KCSAbeywickrama/rgb-g2/enclosure/external parts/push button/Captura de pantalla (63).png

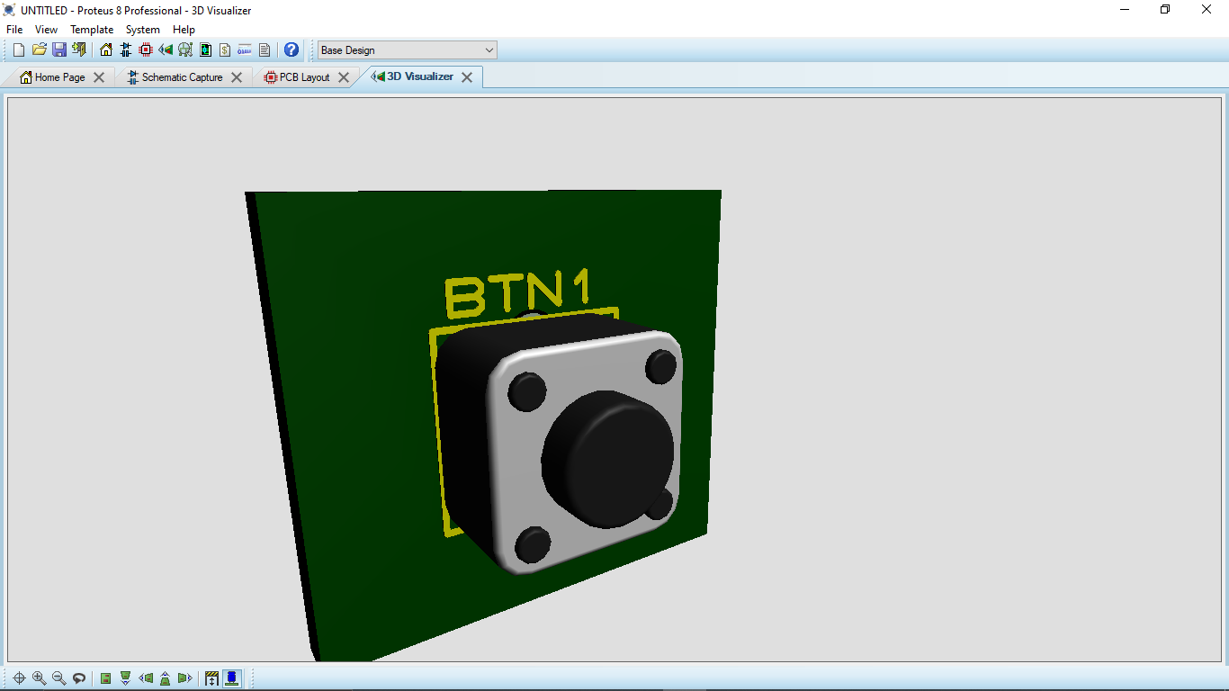
enclosure/external parts/push button/Captura de pantalla (63).png
