KCSAbeywickrama/rgb-g2/enclosure/external parts/capacitor/10pF Ceramic Disc 2.SLDPRT

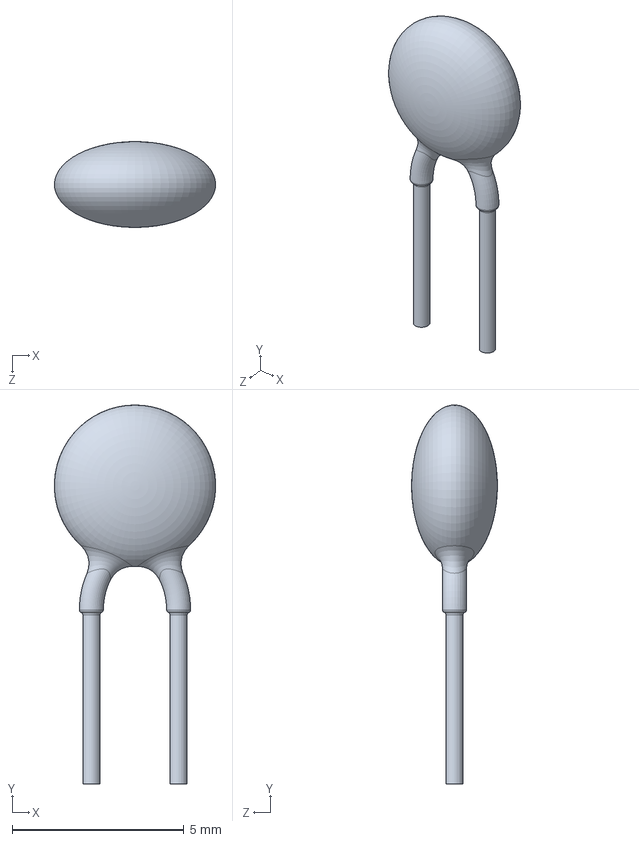
[picture p18: CAD file, 2021-08-13]
enclosure/external parts/capacitor/10pF Ceramic Disc 2.SLDPRT
4.69 x 11.0 x 2.50 mm
