KCSAbeywickrama/rgb-g2/enclosure/external parts/jumper/Converted/ACIS/Wire.step

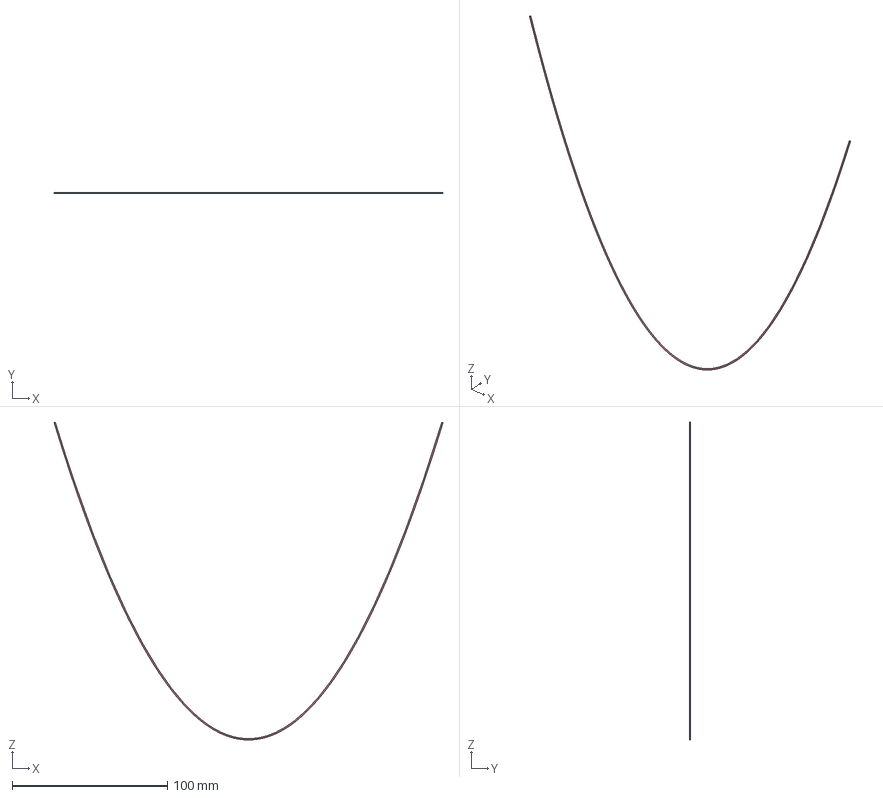
[picture p19: CAD file, 2021-08-13]
enclosure/external parts/jumper/Converted/ACIS/Wire.step
250.8 x 0.9 x 205.0 mm
15cm
20cm
30cm
50cm
