KCSAbeywickrama/rgb-g2/enclosure/external parts/power jack/power jack.SLDPRT

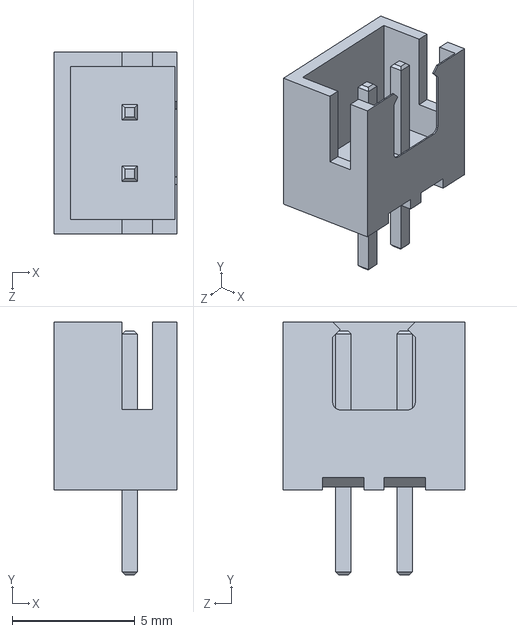
[picture p20: CAD file, 2021-08-13]
enclosure/external parts/power jack/power jack.SLDPRT
5.00 x 10.3 x 7.43 mm
