KCSAbeywickrama/rgb-g2/enclosure/external parts/push button/2_pin_push_button.SLDPRT

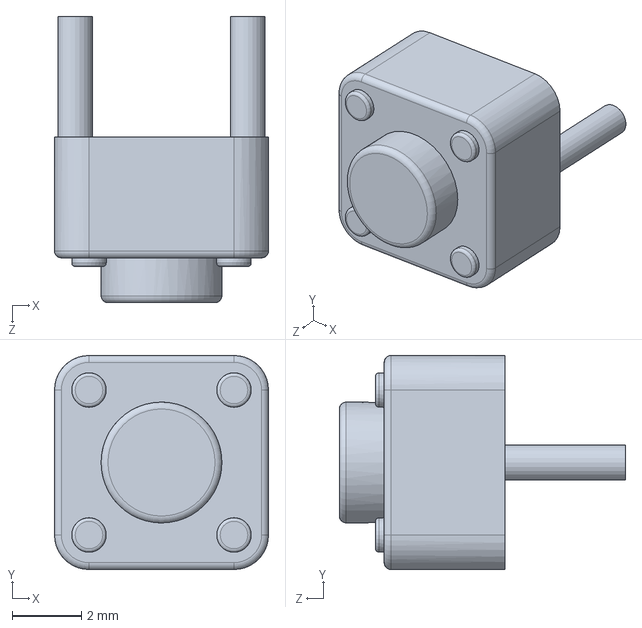
[picture p21: CAD file, 2021-08-13]
enclosure/external parts/push button/2_pin_push_button.SLDPRT
6.20 x 6.20 x 8.30 mm
