KCSAbeywickrama/rgb-g2/enclosure/external parts/rgb led/rgb_led.SLDPRT

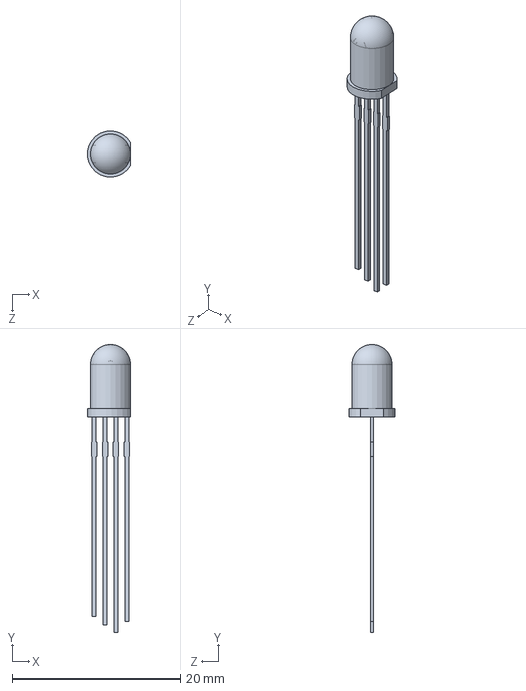
[picture p22: CAD file, 2021-08-13]
enclosure/external parts/rgb led/rgb_led.SLDPRT
5.10 x 34.2 x 5.49 mm
