KCSAbeywickrama/rgb-g2/enclosure/external parts/solder.SLDPRT

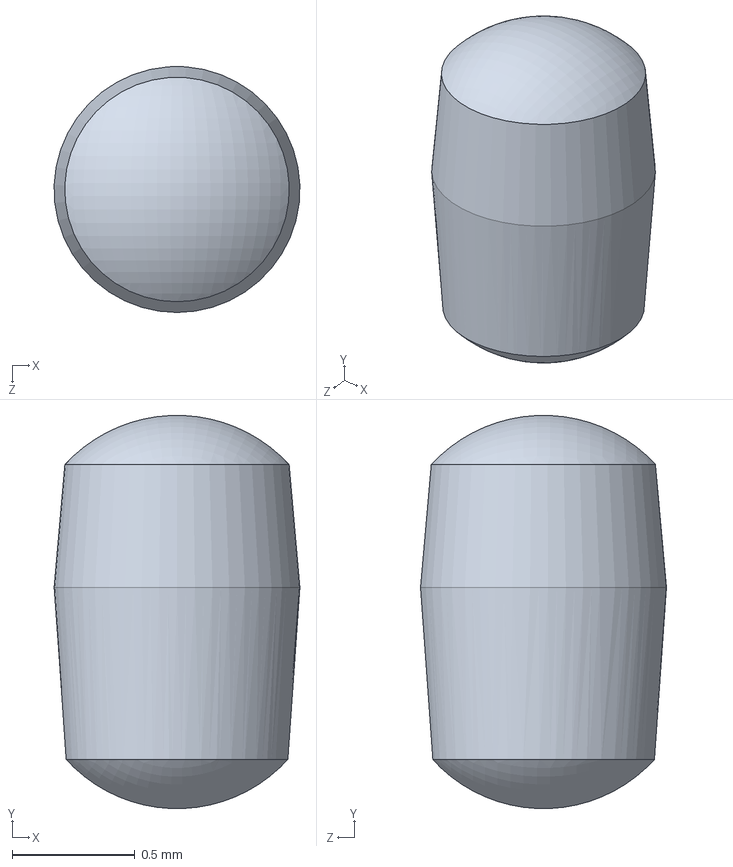
[picture p23: CAD file, 2021-08-13]
enclosure/external parts/solder.SLDPRT
0.999 x 1.60 x 1.00 mm
