KCSAbeywickrama/rgb-g2/enclosure/Model_2_upper_stp.STEP

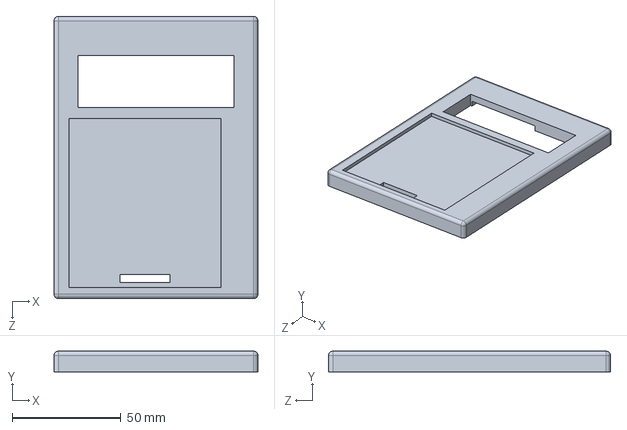
[picture p24: CAD file, 2021-08-13]
enclosure/Model_2_upper_stp.STEP
94.0 x 9.50 x 130.0 mm
