KCSAbeywickrama/rgb-g2/enclosure/Sensor/Sensor_Top.STEP

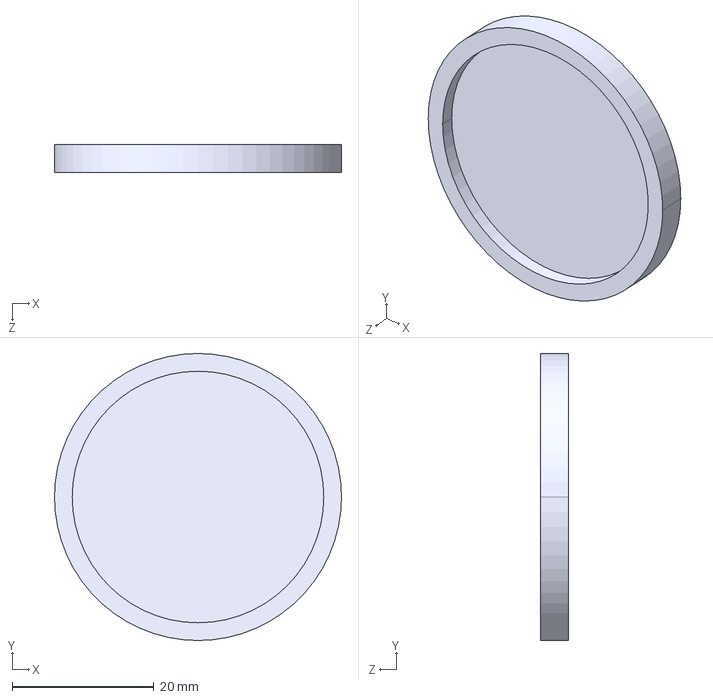
[picture p25: CAD file, 2021-08-13]
enclosure/Sensor/Sensor_Top.STEP
40.5 x 40.5 x 4.00 mm
