KCSAbeywickrama/rgb-g2/pcb_design/STEP files/HDR1X6.STEP

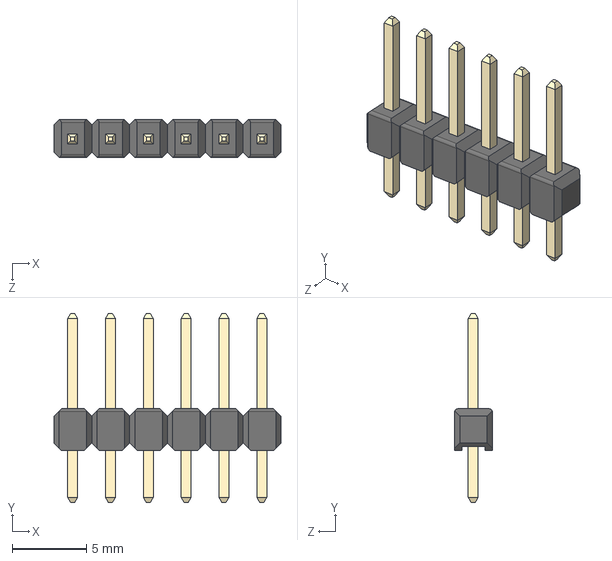
[picture p26: CAD file, 2021-08-13]
pcb_design/STEP files/HDR1X6.STEP
15.2 x 12.7 x 2.54 mm
