KCSAbeywickrama/rgb-g2/enclosure/12X/sensor_model_1_p1.SLDPRT

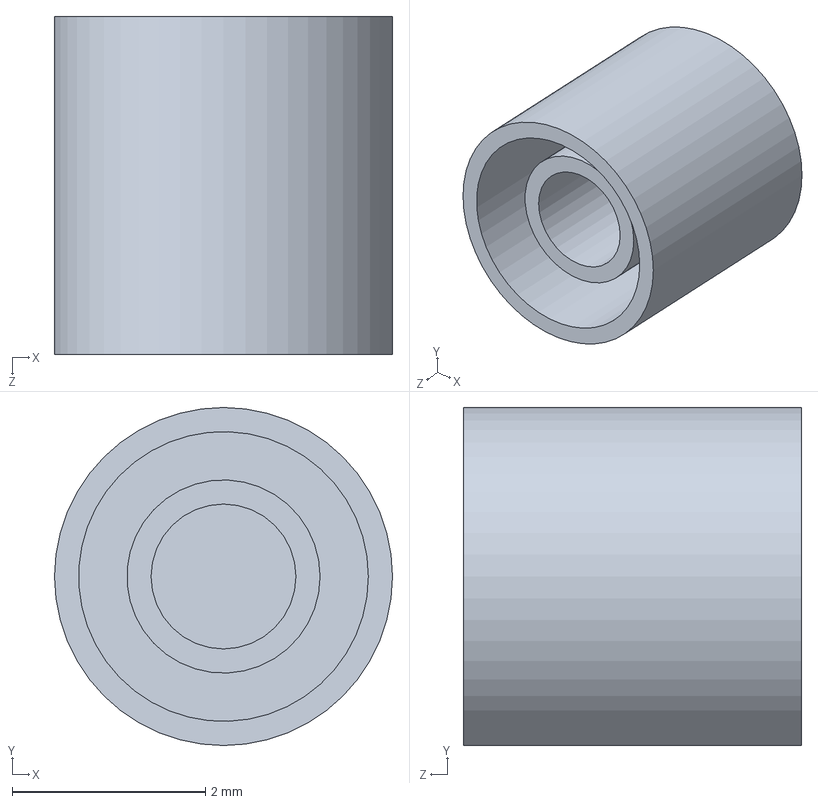
[picture p27: CAD file, 2021-08-06]
enclosure/12X/sensor_model_1_p1.SLDPRT
3.50 x 3.50 x 3.50 mm
