KCSAbeywickrama/rgb-g2/enclosure/enclosure_missed/parts/lcd/LCDScreen.SLDPRT

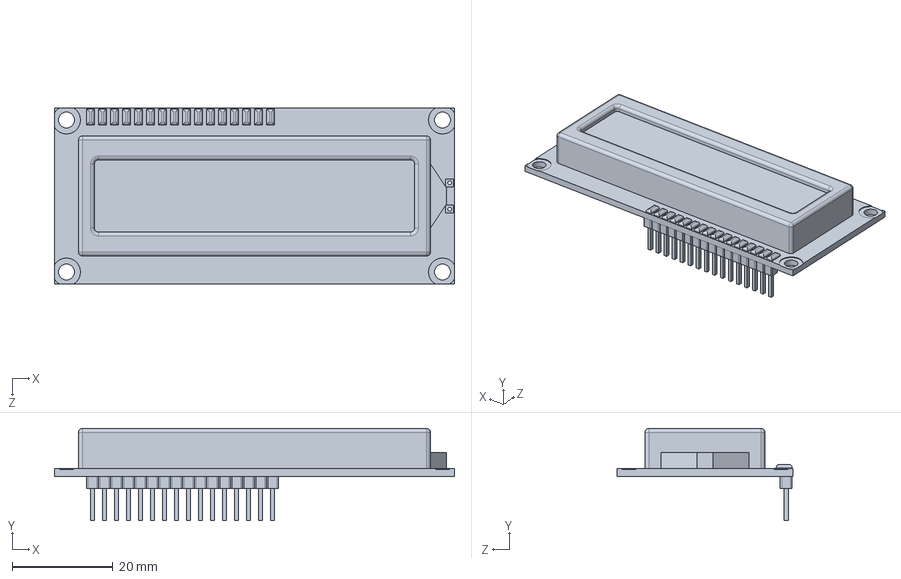
[picture p28: CAD file, 2021-08-13]
enclosure/enclosure_missed/parts/lcd/LCDScreen.SLDPRT
79.4 x 18.3 x 34.9 mm
