KCSAbeywickrama/rgb-g2/enclosure/external parts/jumper/Converted/ACIS/Patterned.step

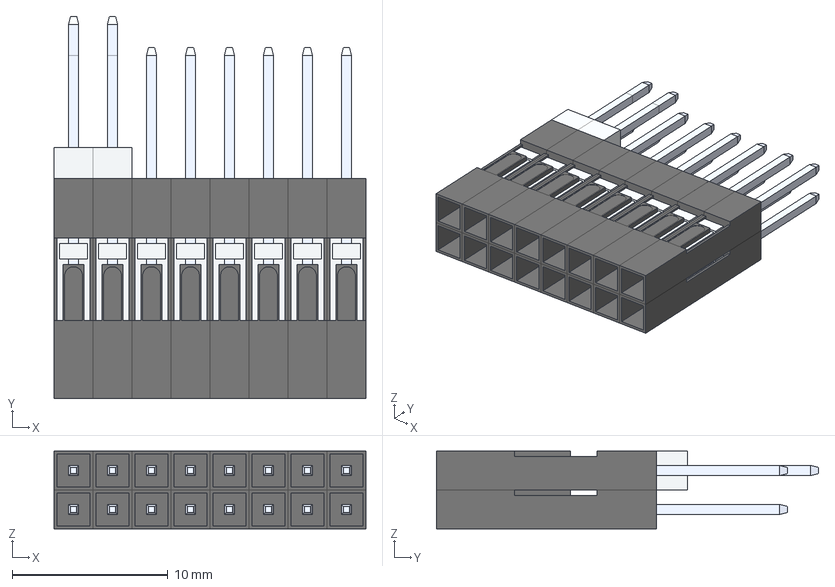
[picture p29: CAD file, 2021-08-13]
enclosure/external parts/jumper/Converted/ACIS/Patterned.step
20.0 x 24.5 x 5.00 mm
Socket-3 x 19
Pin-5 x 20
Socket-5 x 5
Pin-header
Pin-blok
Pin
Header
Blok
Blok-header
