KCSAbeywickrama/rgb-g2/enclosure/external parts/jumper/Converted/STEP/Jumper.step

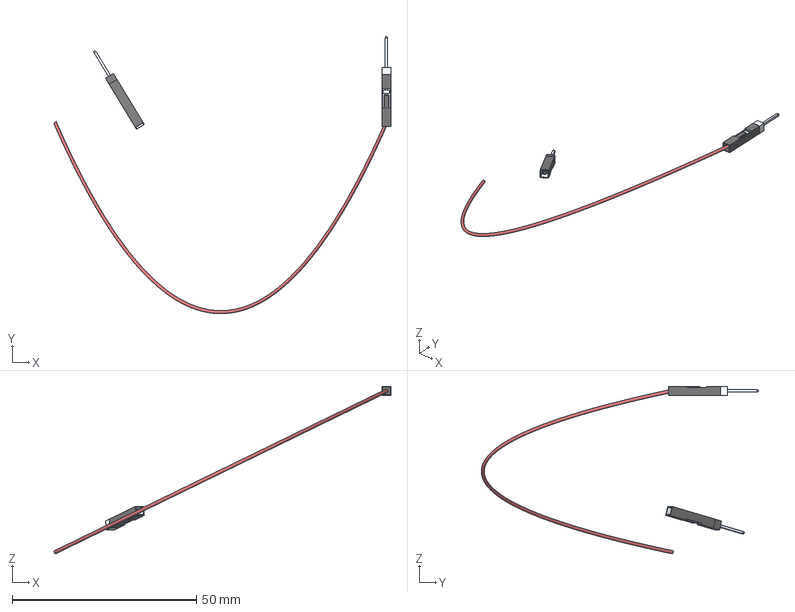
[picture p30: CAD file, 2021-08-13]
enclosure/external parts/jumper/Converted/STEP/Jumper.step
91.5 x 75.3 x 45.5 mm
Pin-1 x 2
Socket-1 x 2
Socket-2
Wire-1
Socket-5
Male-female
Male-female-wire-female
Male-female-wire-female-male
Male-female-wire-female/15 cm Male-female-wire-female
Male-female-wire-female/20cm Male-female-wire-female
Male-female-wire-female/30cm Male-female-wire-female
Male-female-wire-female/50cm Male-female-wire-female
Male-female-wire-female-male/15cm Male-female-wire-female-male
Male-female-wire-female-male/20cm Male-female-wire-female-male
Male-female-wire-female-male/30cm Male-female-wire-female-male
Male-female-wire-female-male/50cm Male-female-wire-female-male
