KCSAbeywickrama/rgb-g2/enclosure/external parts/rgb led/CA GRB LED 5mm.STEP

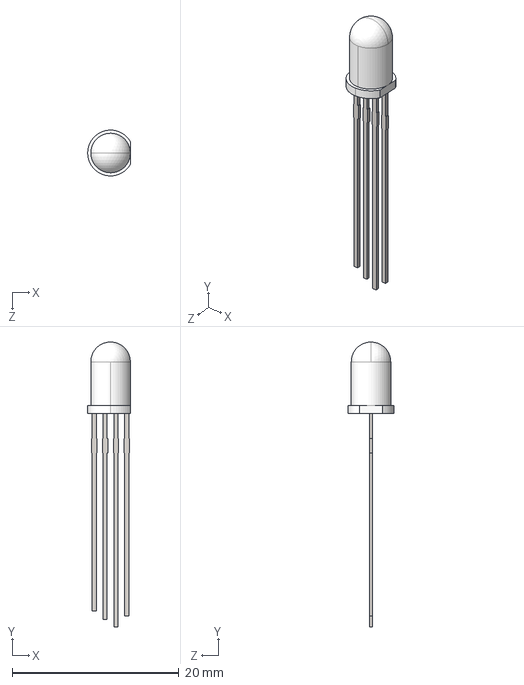
[picture p31: CAD file, 2021-08-13]
enclosure/external parts/rgb led/CA GRB LED 5mm.STEP
5.12 x 34.2 x 5.50 mm
