KCSAbeywickrama/rgb-g2/enclosure/external parts/solder 2.SLDPRT

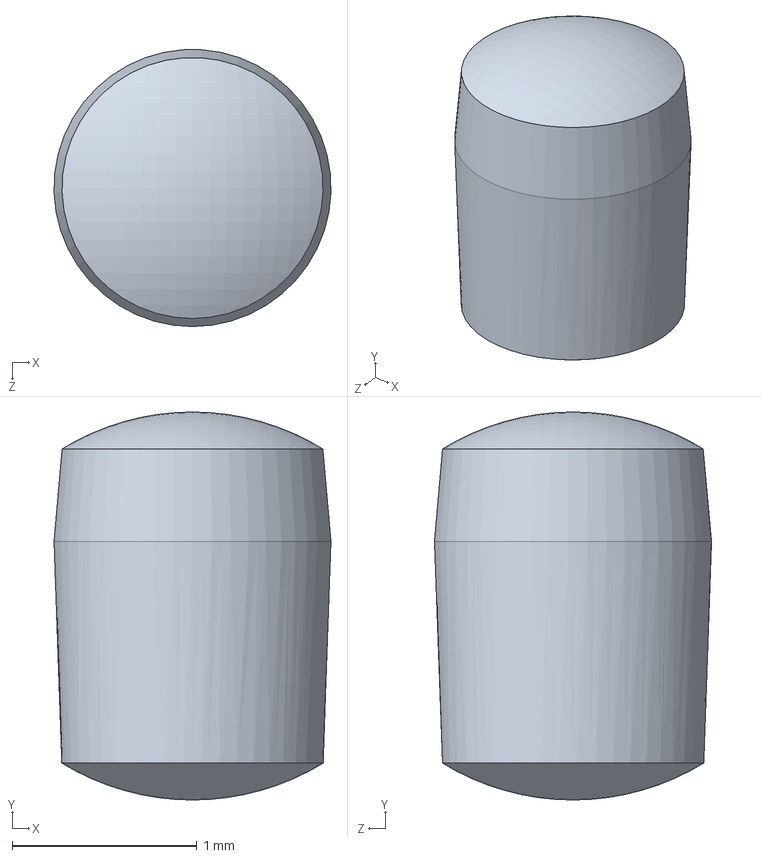
[picture p32: CAD file, 2021-08-13]
enclosure/external parts/solder 2.SLDPRT
1.50 x 2.10 x 1.50 mm
