KCSAbeywickrama/rgb-g2/pcb_design/STEP files/HDR1X8.STEP

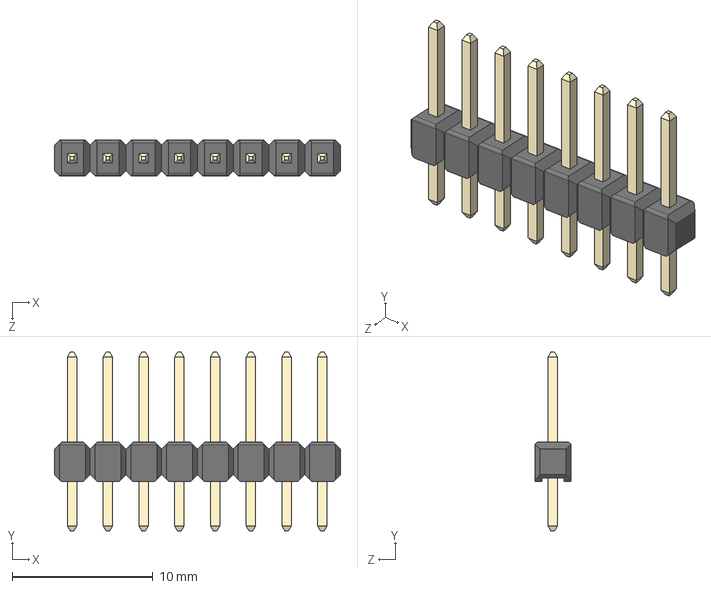
[picture p33: CAD file, 2021-08-13]
pcb_design/STEP files/HDR1X8.STEP
20.3 x 12.7 x 2.54 mm
