KCSAbeywickrama/rgb-g2/enclosure/12X/sensor_model_1_p2.SLDPRT

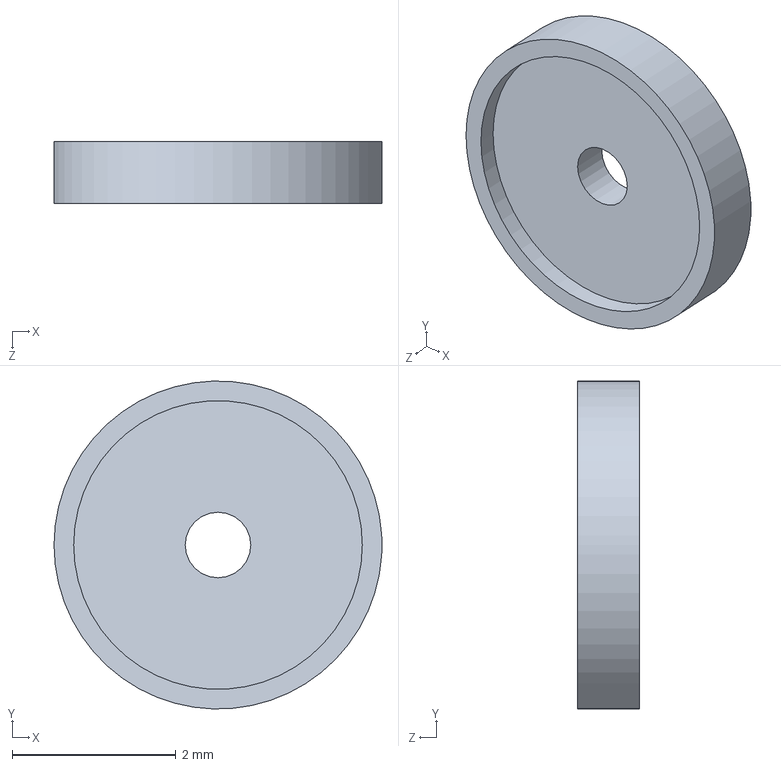
[picture p34: CAD file, 2021-08-06]
enclosure/12X/sensor_model_1_p2.SLDPRT
4.00 x 4.00 x 0.75 mm
