KCSAbeywickrama/rgb-g2/enclosure/enclosure parts/bottom_part.SLDPRT

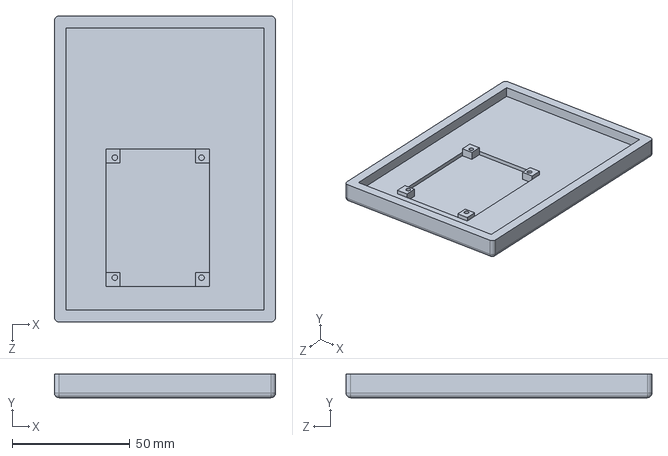
[picture p35: CAD file, 2021-08-13]
enclosure/enclosure parts/bottom_part.SLDPRT
94.0 x 10.0 x 130.0 mm
