KCSAbeywickrama/rgb-g2/enclosure/enclosure_missed/UPPER__FROM_STEP.SLDPRT

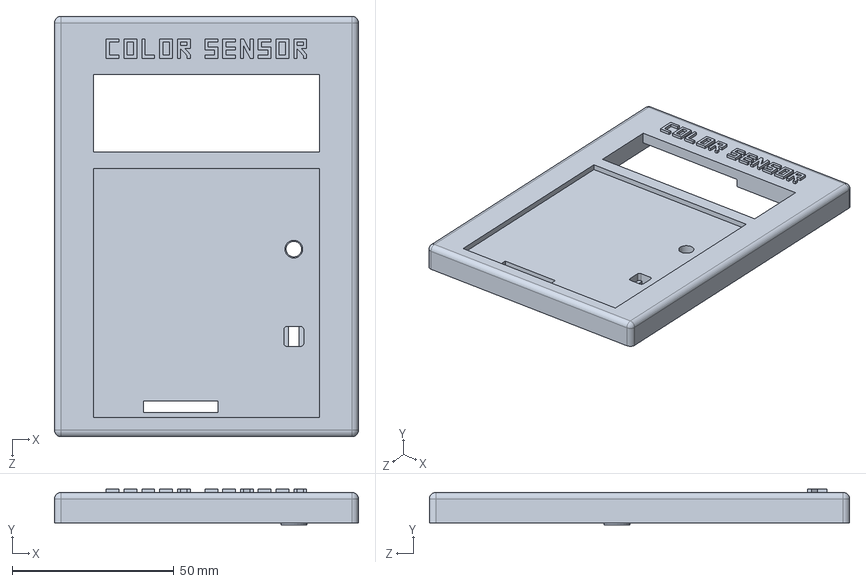
[picture p36: CAD file, 2021-08-13]
enclosure/enclosure_missed/UPPER__FROM_STEP.SLDPRT
94.0 x 11.0 x 130.0 mm
