KCSAbeywickrama/rgb-g2/enclosure/external parts/jumper/Pin.SLDPRT

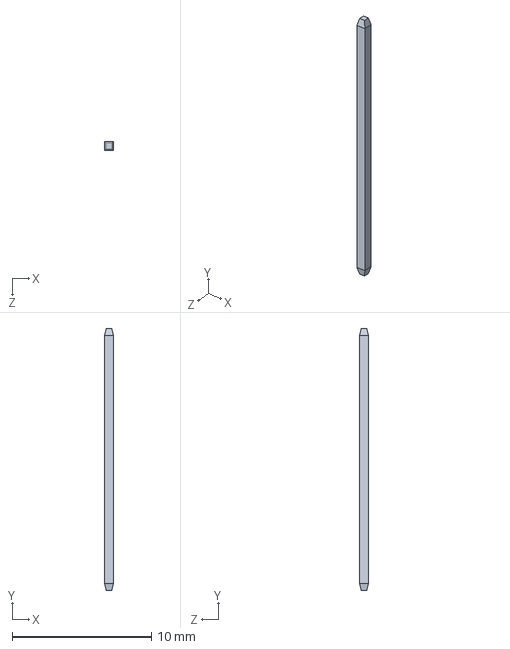
[picture p37: CAD file, 2021-08-13]
enclosure/external parts/jumper/Pin.SLDPRT
0.65 x 18.8 x 0.65 mm
