KCSAbeywickrama/rgb-g2/pcb_design/STEP files/HDR1X4.STEP

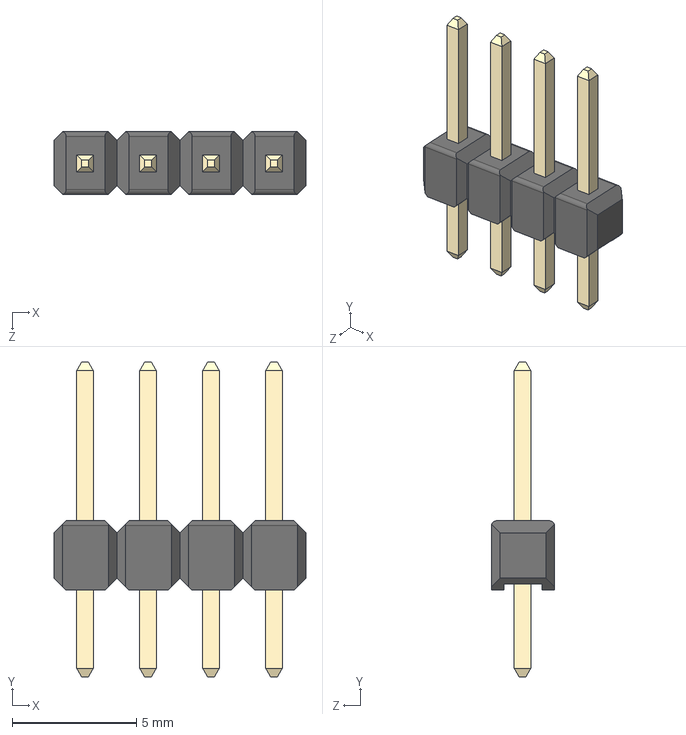
[picture p38: CAD file, 2021-08-13]
pcb_design/STEP files/HDR1X4.STEP
10.2 x 12.7 x 2.54 mm
