KCSAbeywickrama/rgb-g2/enclosure/21A_upper.SLDPRT

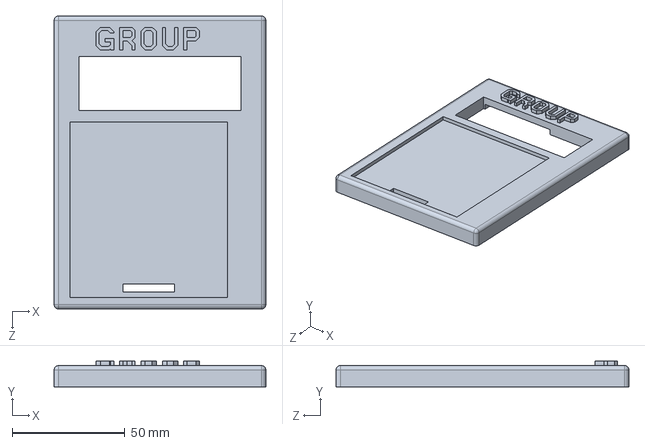
[picture p39: CAD file, 2021-08-13]
enclosure/21A_upper.SLDPRT
94.0 x 11.5 x 130.0 mm
