KCSAbeywickrama/rgb-g2/enclosure/enclosure_missed/sensor_holder.SLDPRT

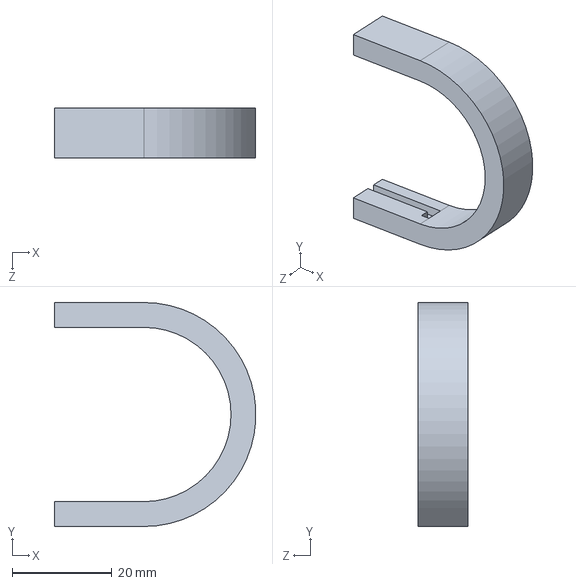
[picture p40: CAD file, 2021-08-13]
enclosure/enclosure_missed/sensor_holder.SLDPRT
40.5 x 45.0 x 10.00 mm
