KCSAbeywickrama/rgb-g2/enclosure/external parts/copper wire.SLDPRT

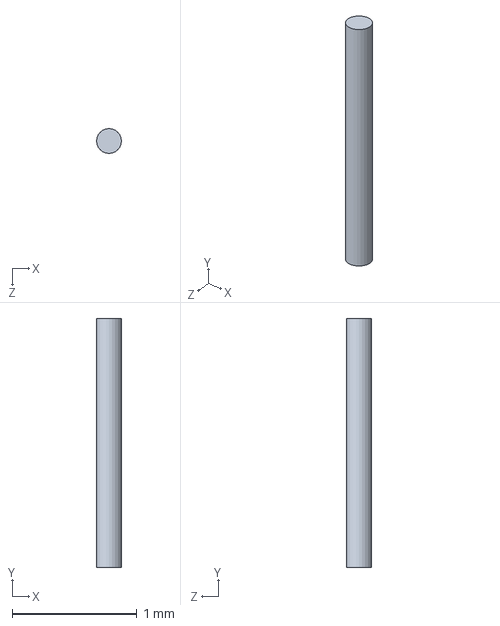
[picture p41: CAD file, 2021-08-13]
enclosure/external parts/copper wire.SLDPRT
0.2 x 2.00 x 0.2 mm
