KCSAbeywickrama/rgb-g2/enclosure/external parts/jumper/Socket_lcd.SLDPRT

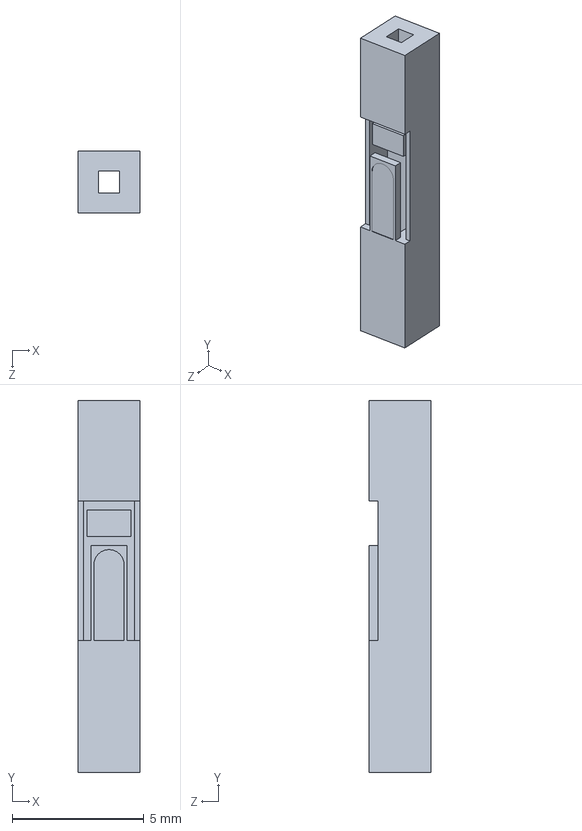
[picture p42: CAD file, 2021-08-13]
enclosure/external parts/jumper/Socket_lcd.SLDPRT
2.35 x 14.1 x 2.35 mm
