KCSAbeywickrama/rgb-g2/pcb_design/STEP files/HDR1X2.STEP

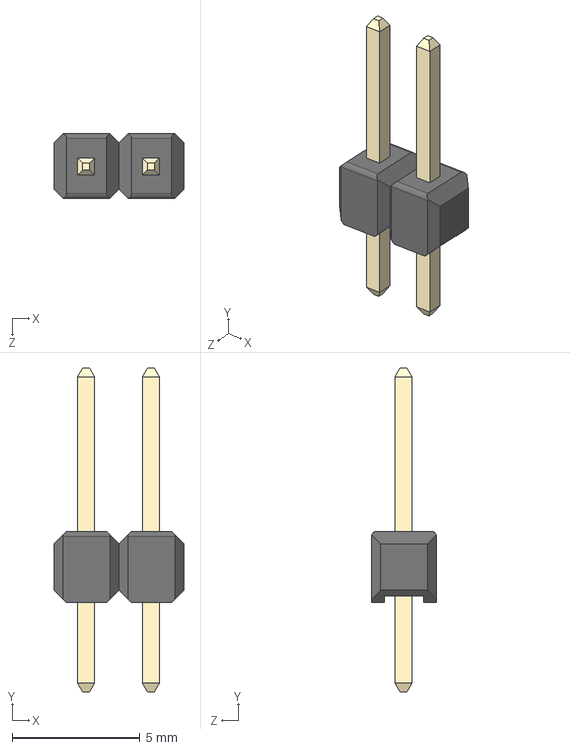
[picture p43: CAD file, 2021-08-13]
pcb_design/STEP files/HDR1X2.STEP
5.08 x 12.7 x 2.54 mm
