KCSAbeywickrama/rgb-g2/enclosure/enclosure_missed/model_1.SLDPRT

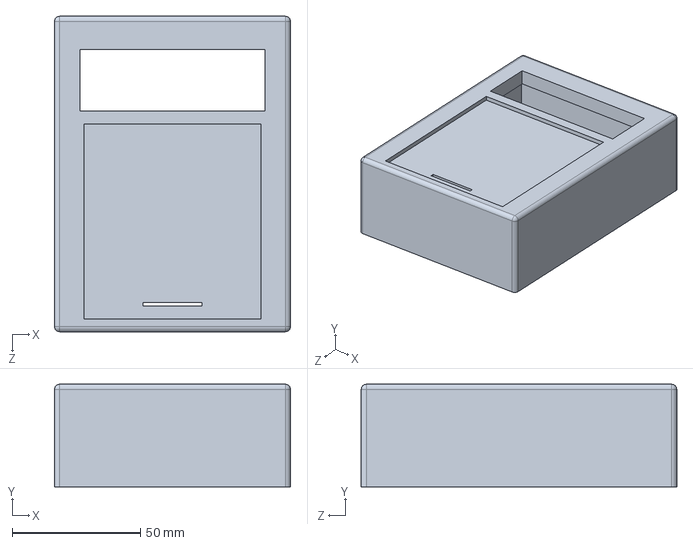
[picture p44: CAD file, 2021-08-06]
enclosure/enclosure_missed/model_1.SLDPRT
92.0 x 40.0 x 123.0 mm
