KCSAbeywickrama/rgb-g2/enclosure/Sensor/sensor_body.STEP

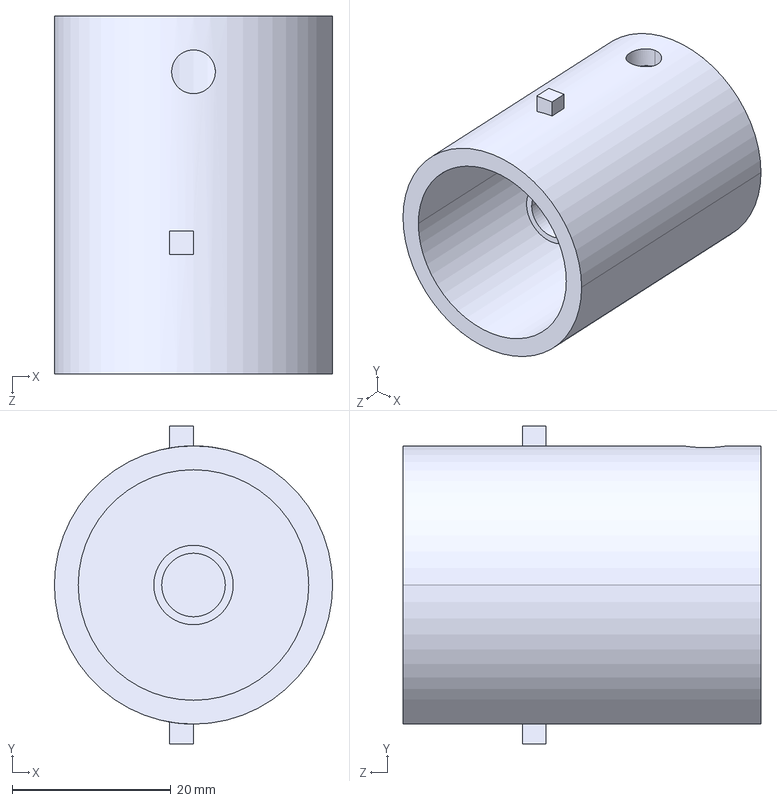
[picture p45: CAD file, 2021-08-13]
enclosure/Sensor/sensor_body.STEP
35.0 x 40.0 x 45.0 mm
