KCSAbeywickrama/rgb-g2/pcb_design/STEP files/HDR1X1.STEP

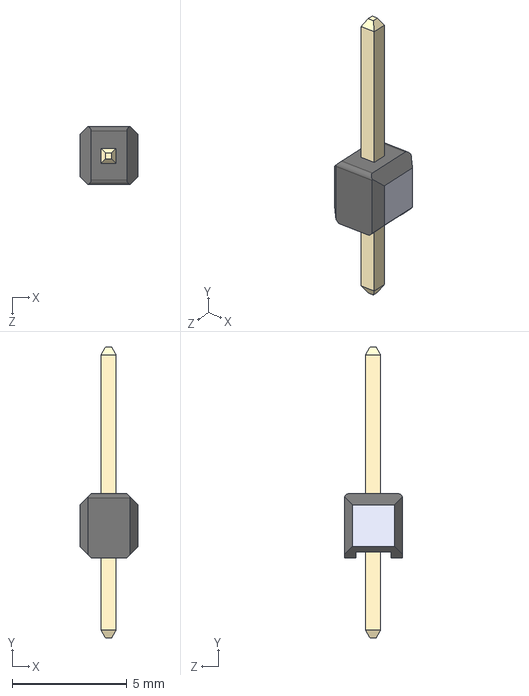
[picture p46: CAD file, 2021-08-13]
pcb_design/STEP files/HDR1X1.STEP
2.54 x 12.7 x 2.54 mm
