KCSAbeywickrama/rgb-g2/enclosure/enclosure_missed/Model_2_upper.SLDPRT

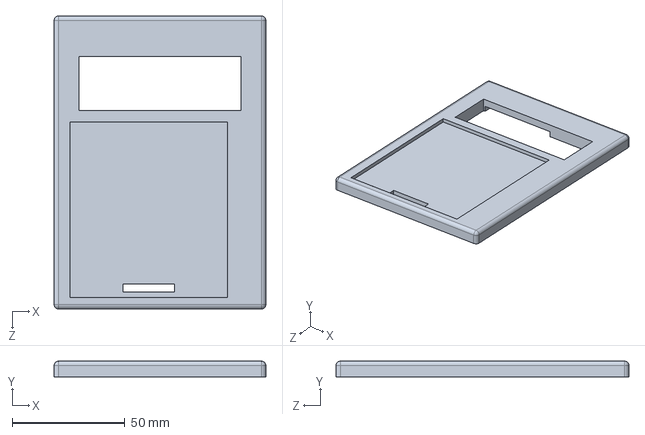
[picture p47: CAD file, 2021-08-06]
enclosure/enclosure_missed/Model_2_upper.SLDPRT
94.0 x 7.00 x 130.0 mm
