KCSAbeywickrama/rgb-g2/enclosure/external parts/jumper/Wire.SLDPRT

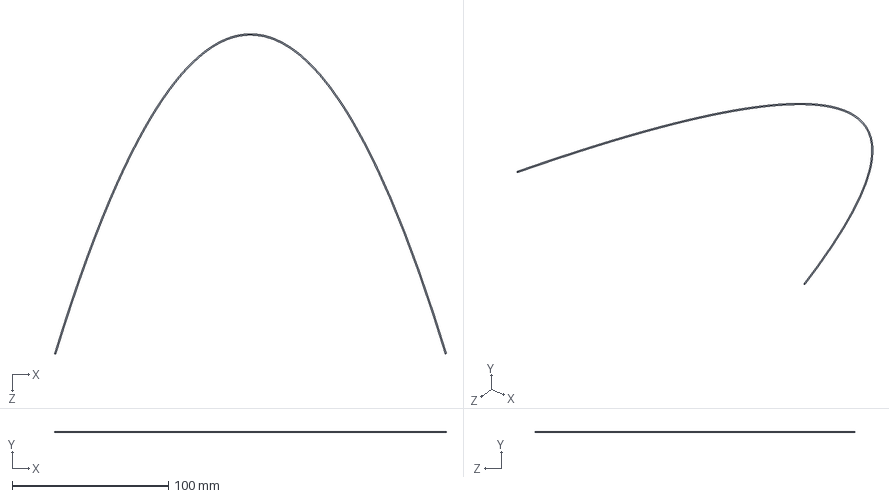
[picture p48: CAD file, 2021-08-13]
enclosure/external parts/jumper/Wire.SLDPRT
250.8 x 0.9 x 205.0 mm
