KCSAbeywickrama/rgb-g2/enclosure/Sensor/PCB_Sensor (2).step

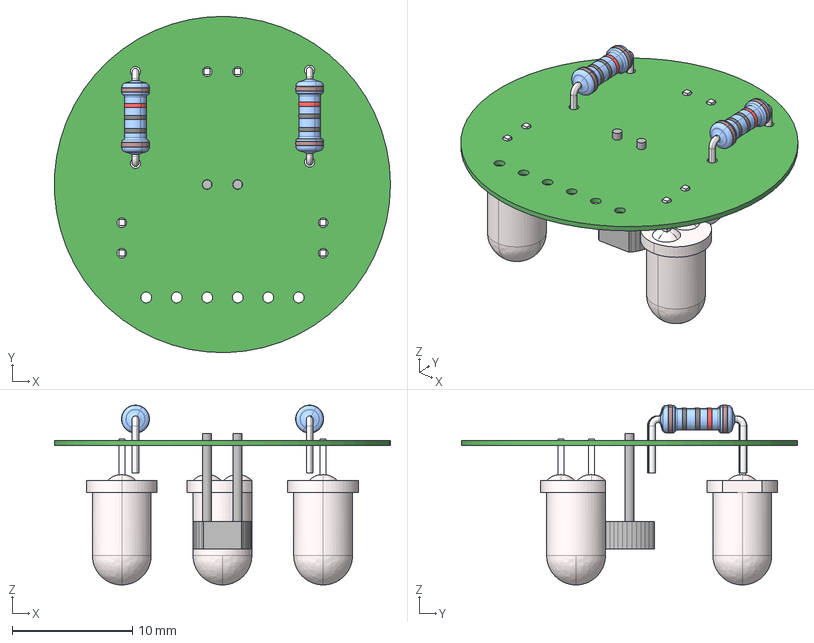
[picture p49: CAD file, 2021-08-13]
enclosure/Sensor/PCB_Sensor (2).step
28.0 x 28.0 x 15.0 mm
Resistor_10K_Ohm_tol1pct_0,25W__07,62 x 2
LED_5mm_white_TH x 3
Extruded
