KCSAbeywickrama/rgb-g2/pcb_design/STEP files/HDR1X7.STEP

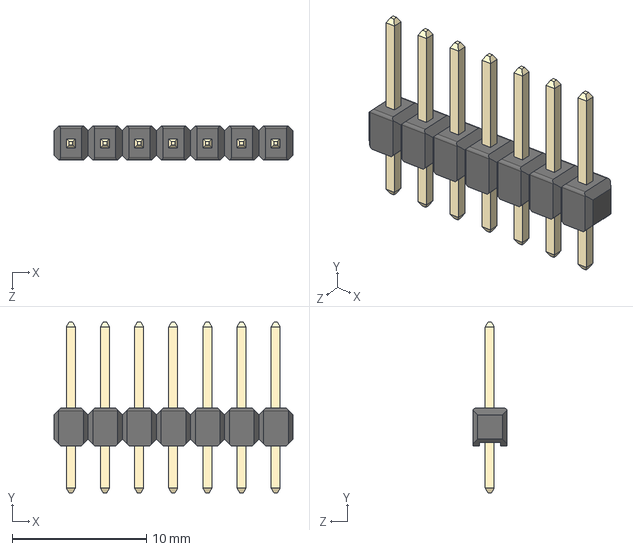
[picture p50: CAD file, 2021-08-13]
pcb_design/STEP files/HDR1X7.STEP
17.8 x 12.7 x 2.54 mm
