KCSAbeywickrama/rgb-g2/enclosure/enclosure parts/circular_leg.SLDPRT

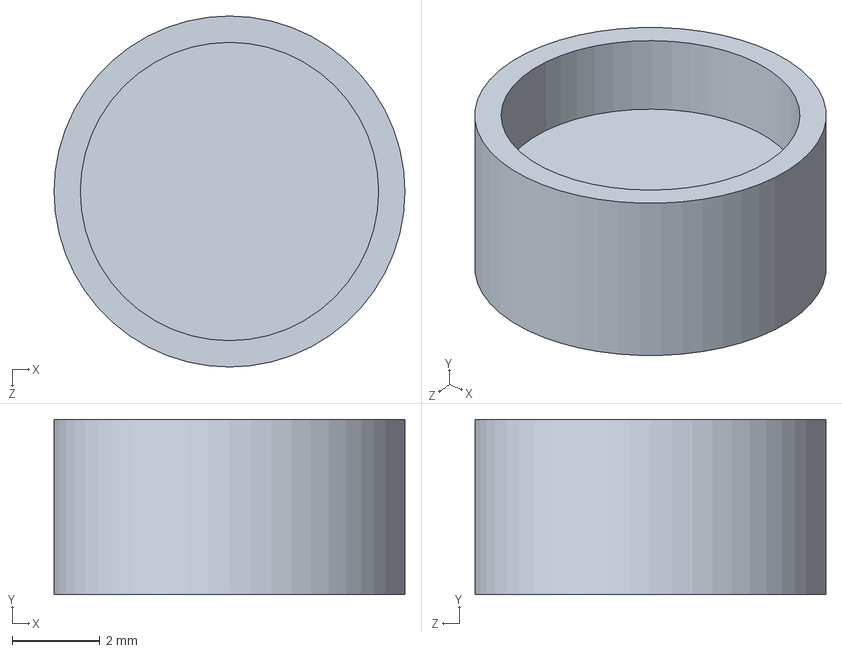
[picture p51: CAD file, 2021-08-13]
enclosure/enclosure parts/circular_leg.SLDPRT
8.00 x 4.00 x 8.00 mm
