KCSAbeywickrama/rgb-g2/enclosure/enclosure_missed/Model_2_middle.SLDPRT

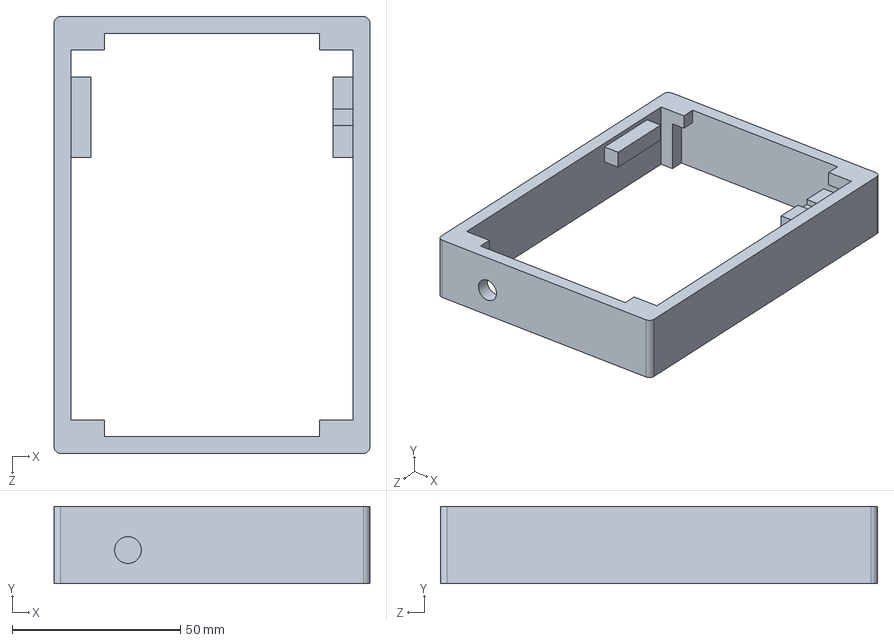
[picture p52: CAD file, 2021-08-06]
enclosure/enclosure_missed/Model_2_middle.SLDPRT
94.0 x 23.0 x 130.0 mm
