KCSAbeywickrama/rgb-g2/pcb_design/STEP files/Led 5 mm.STEP

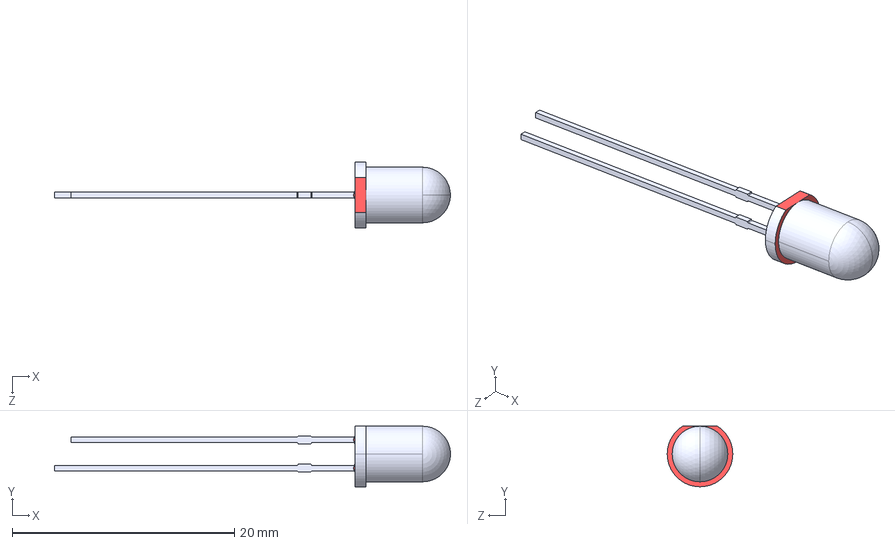
[picture p53: CAD file, 2021-08-13]
pcb_design/STEP files/Led 5 mm.STEP
35.6 x 5.45 x 5.90 mm
