KCSAbeywickrama/rgb-g2/enclosure/enclosure parts/sensor_model1.STEP

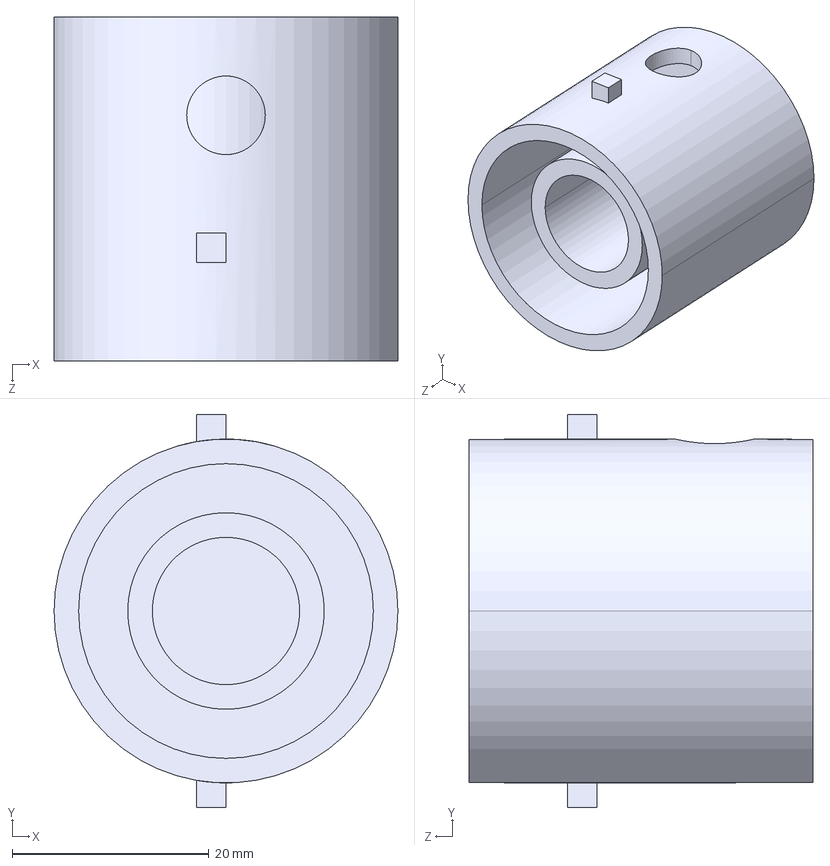
[picture p54: CAD file, 2021-08-13]
enclosure/enclosure parts/sensor_model1.STEP
35.0 x 40.0 x 35.0 mm
