KCSAbeywickrama/rgb-g2/pcb_design/STEP files/Cap3.STEP

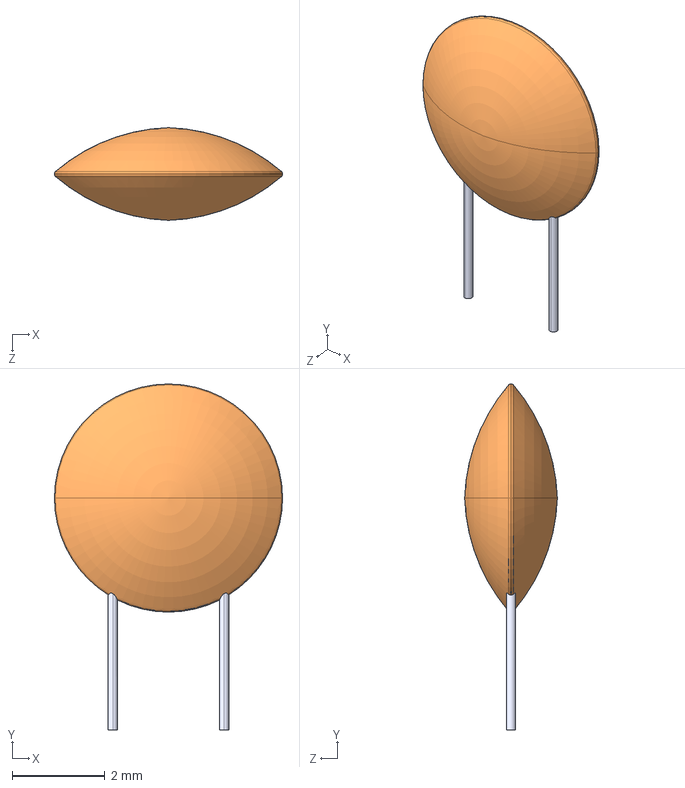
[picture p55: CAD file, 2021-08-13]
pcb_design/STEP files/Cap3.STEP
4.92 x 7.46 x 2.00 mm
